agysft/TempSensor/image/04-01.png

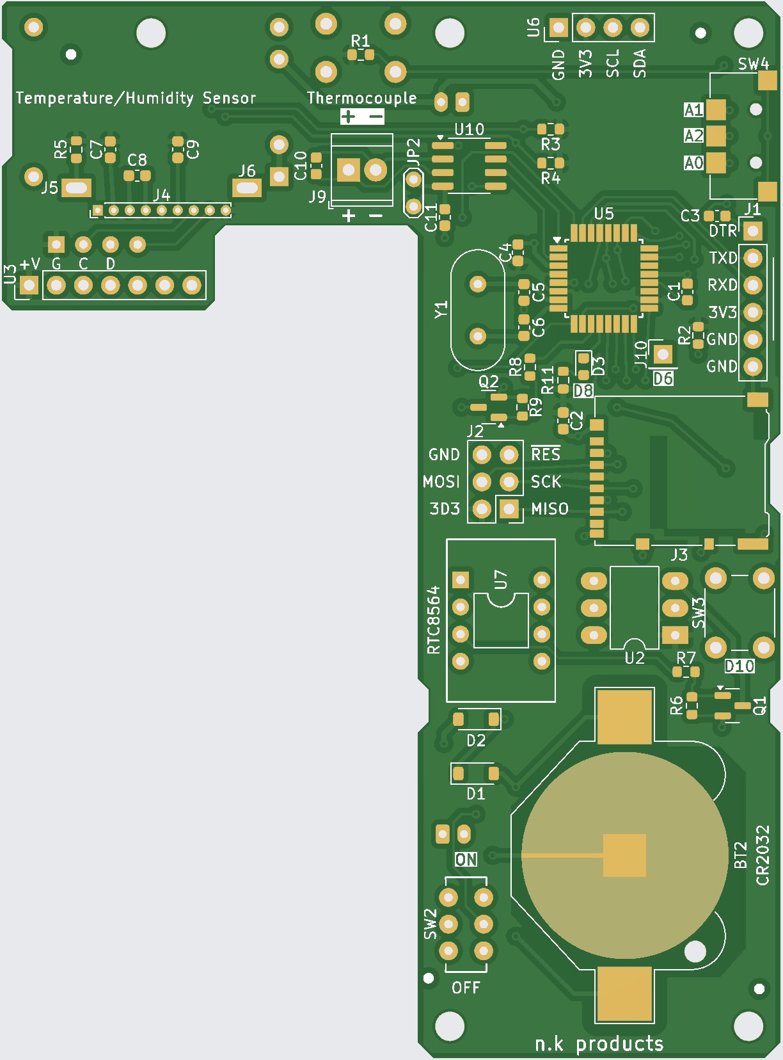
image/04-01.png
