agysft/TempSensor/image/04-02.png

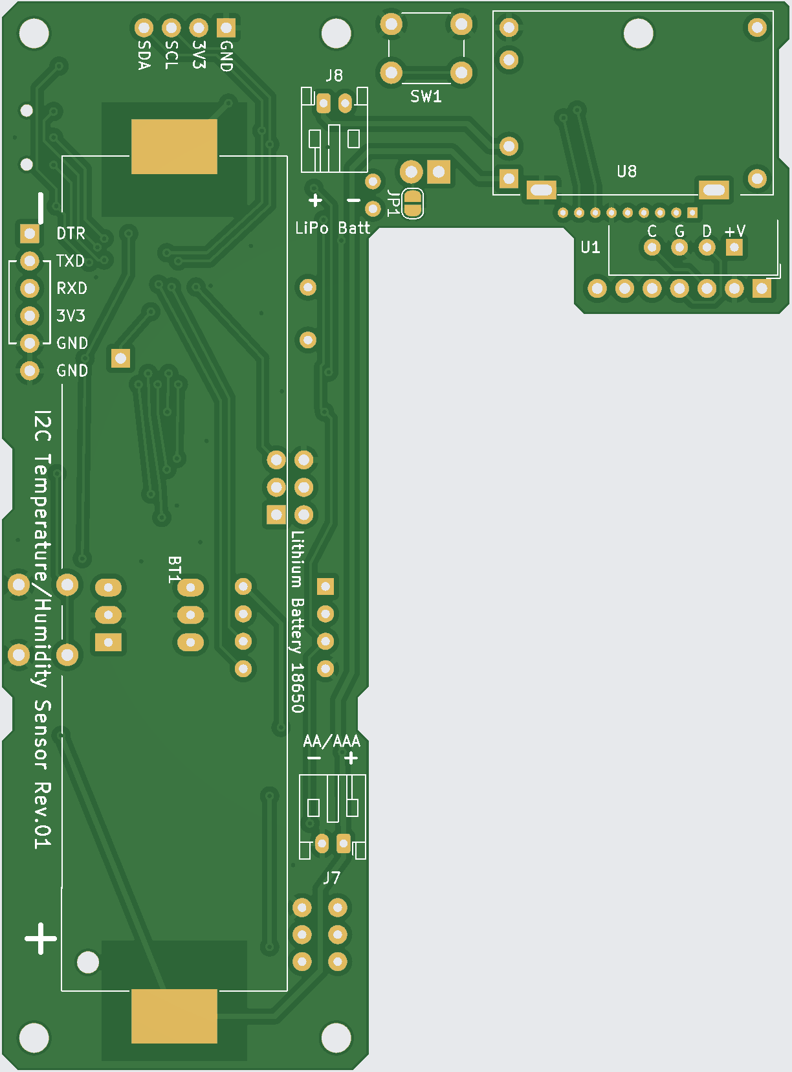
image/04-02.png
